brucemack/kc1fsz-rc1/hw/if-2/sim/out2.asc

C1: cap; 4.7µ
C2: cap; 470p
C3: cap; 10µ
C4: cap; 100p
C5: cap; 4.7µ
C6: cap; 10µ
R1: res; 20k
R2: res; 100k
R3: res; 10k
R4: res; 510
R5: res; 1k
R6: res; 20k
R7: res; 20k
R8: res; 25k
R9: res; 25k
U1: UniversalOpAmp
U2: UniversalOpAmp
V1: voltage; SINE(0 0.75 1000); AC 1; Rser=600
V2: battery; 2.5
V3: battery; 5
Named nets: 0, Vout, Vin, Vbias, Vcc, Vo
.tran 10m
.ac oct 32 60 2000
Digital Repeater 2 - Audio Output Network
