brucemack/kc1fsz-rc1/hw/if-2/sim/in1.asc

C1: cap; 4.7µ
C2: cap; 4.7µ
C3: cap; 1800p
C4: cap; 1800p
C5: cap; 0.01µ
C6: cap; 4.7µ
C7: cap; 4.7µ
C8: cap; 0.001µ
R1: res; 20k
R2: res; 100k
R3: res; 4.7k
R4: res; 4.7k
R5: res; 10k
R6: res; 1k
R7: res; 1k
R8: res; 47
R9: res; 1k
R10: res; 1k
R11: res; 47
R12: res; 10k
R13: res; 1k
R14: res; 25k
R15: res; 25k
R16: res; 1k
U1: UniversalOpAmp
U2: UniversalOpAmp
U3: UniversalOpAmp
U4: UniversalOpAmp
V1: voltage; SINE(0 0.75 1000); AC 1; Rser=600
V2: battery; 2.5
V3: battery; 5
Named nets: 0, Vout_p, Vin, Vbias, Vcc, Vout_n, Va
.tran 10m
.ac oct 32 60 200000
Digital Repeater 2 - Audio Input Network
Input impedance 
per ADC1804 datasheet.
